BoomerChiao/Arduino_Air-Quality-Monitor/Jpg/3D_casing_A.png

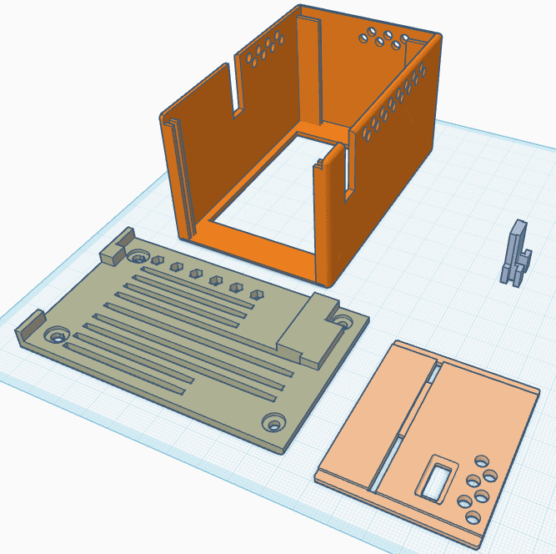
Jpg/3D_casing_A.png
