BoomerChiao/Arduino_Air-Quality-Monitor/Jpg/3D_casing_B.png

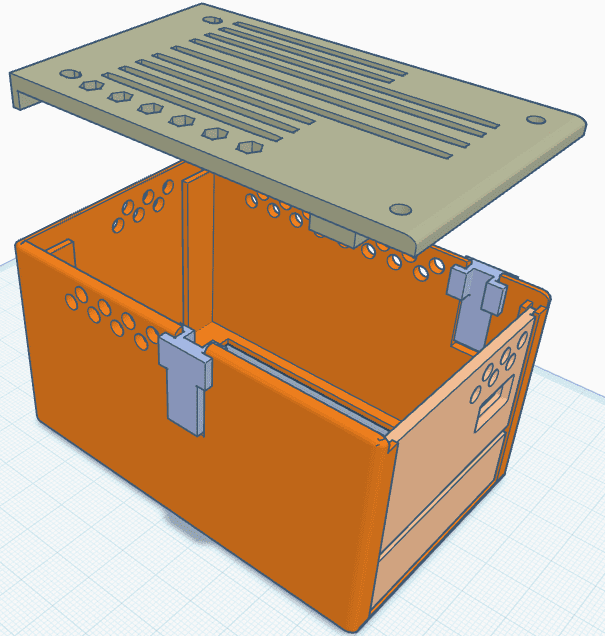
Jpg/3D_casing_B.png
