BoomerChiao/Arduino_Air-Quality-Monitor/Jpg/3D_casing_C.png

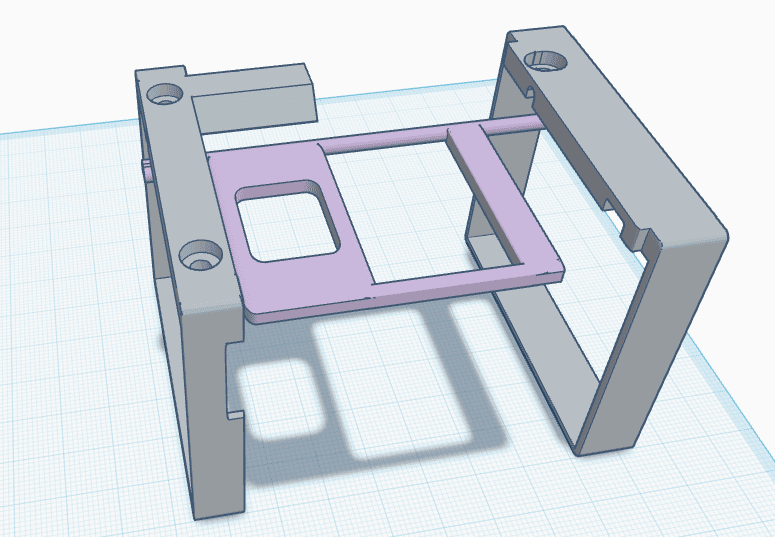
Jpg/3D_casing_C.png
