BoomerChiao/Arduino_Air-Quality-Monitor/Jpg/3D_casing_D.png

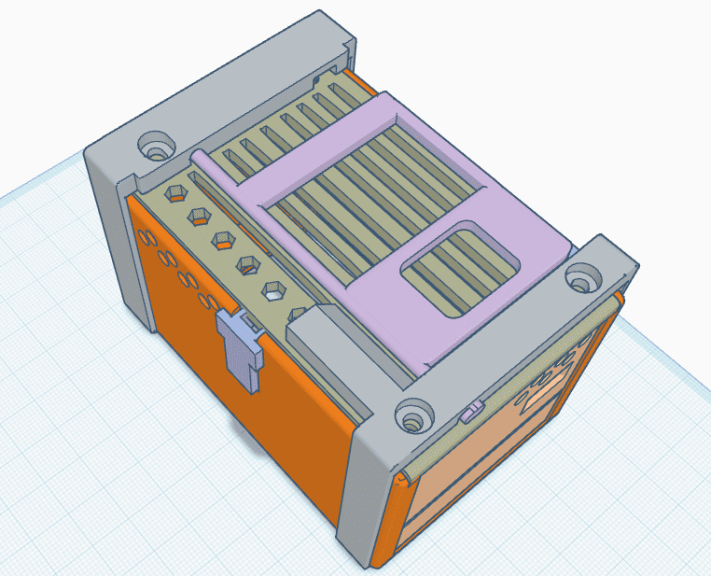
Jpg/3D_casing_D.png
