BoomerChiao/Arduino_Air-Quality-Monitor/Jpg/3D_casing_E.png

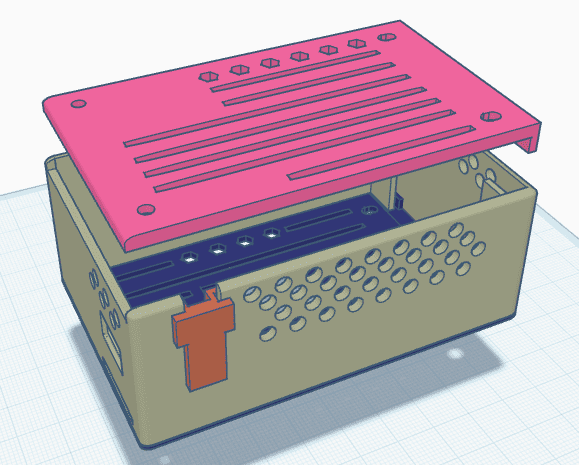
Jpg/3D_casing_E.png
