BoomerChiao/Arduino_Air-Quality-Monitor/Jpg/3D_casing_F.png

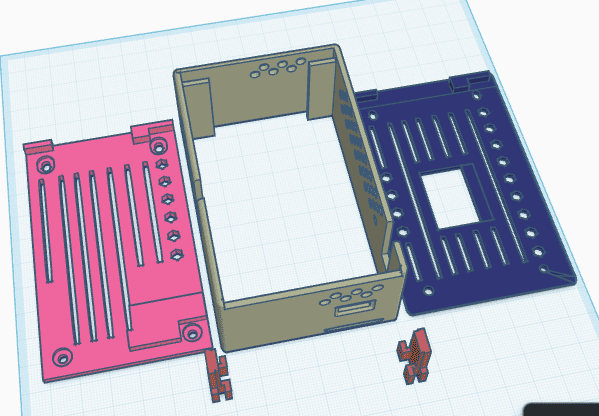
Jpg/3D_casing_F.png
