BoomerChiao/Arduino_Air-Quality-Monitor/Jpg/AHT20.png

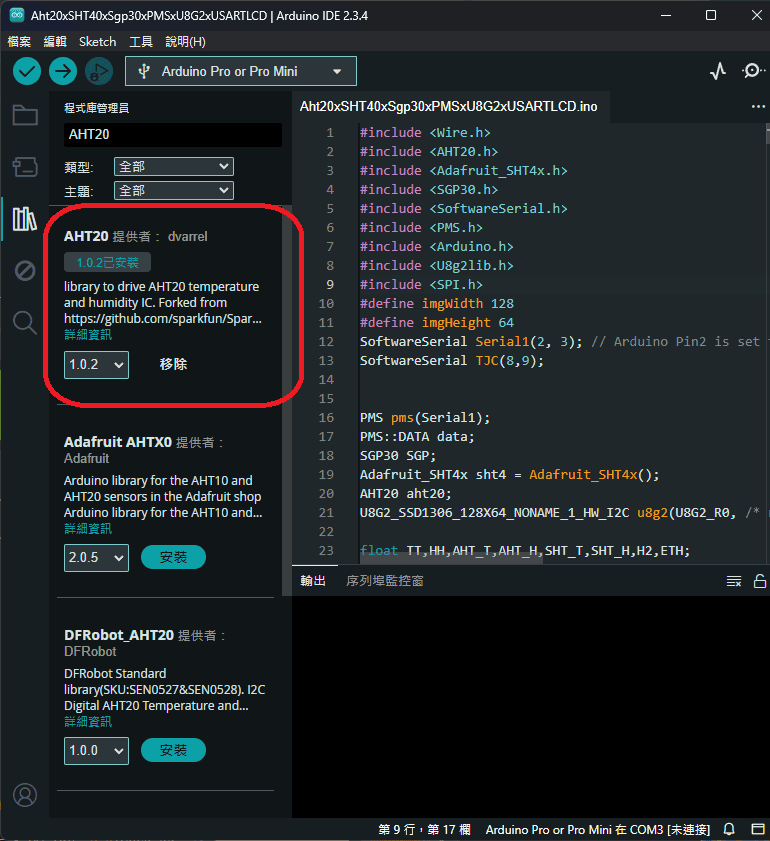
Jpg/AHT20.png
