BoomerChiao/Arduino_Air-Quality-Monitor/Jpg/DEMO/LCD_3d_A.png

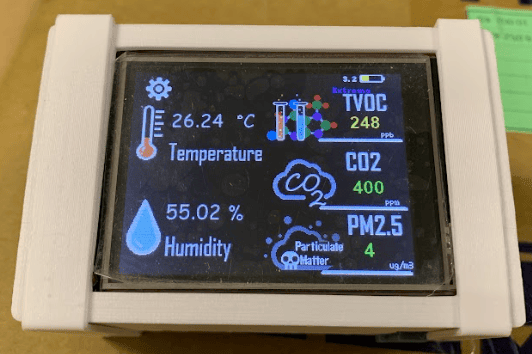
Jpg/DEMO/LCD_3d_A.png
