BoomerChiao/Arduino_Air-Quality-Monitor/Jpg/DEMO/LCD_3d_B.png

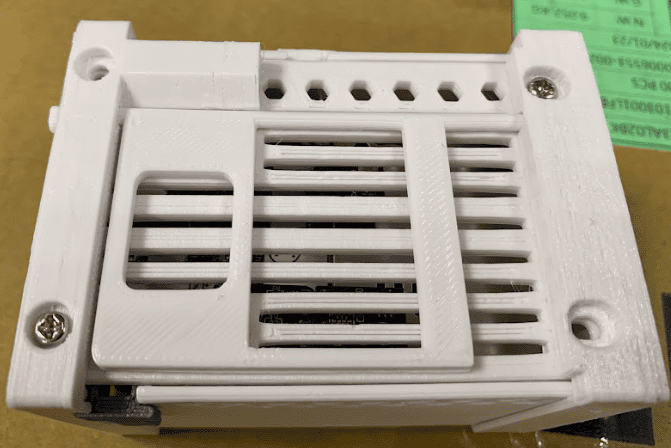
Jpg/DEMO/LCD_3d_B.png
