BoomerChiao/Arduino_Air-Quality-Monitor/Jpg/DEMO/LCD_3d_C.png

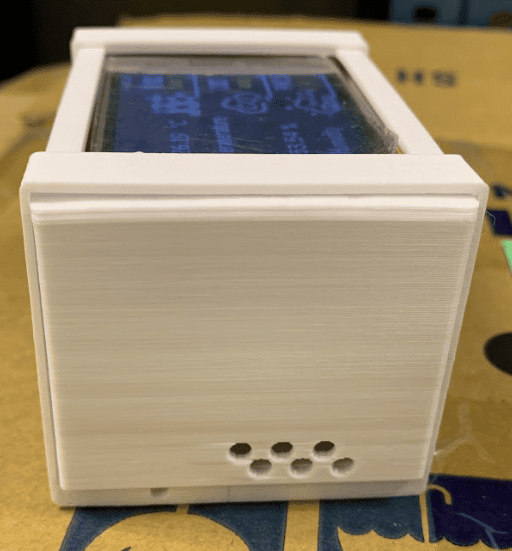
Jpg/DEMO/LCD_3d_C.png
