BoomerChiao/Arduino_Air-Quality-Monitor/Jpg/DEMO/LCD_3d_CD.png

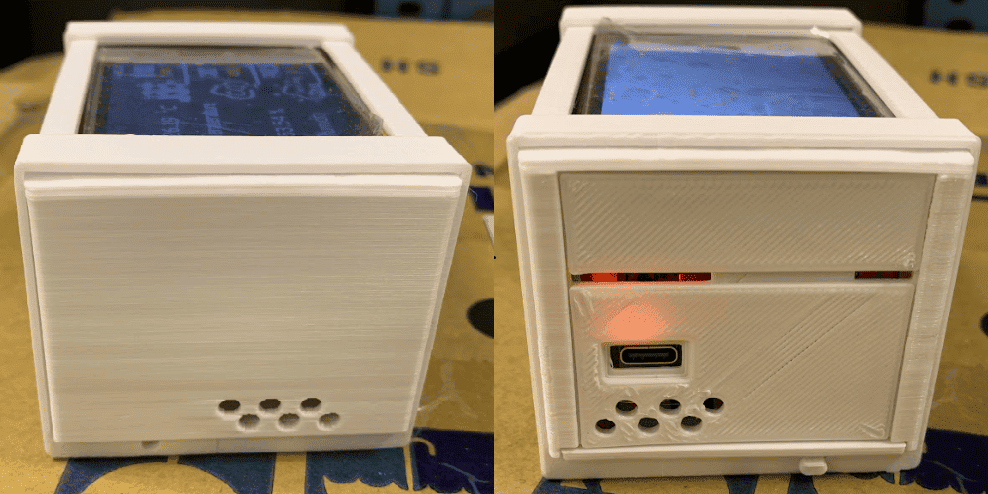
Jpg/DEMO/LCD_3d_CD.png
