BoomerChiao/Arduino_Air-Quality-Monitor/Jpg/DEMO/LCD_3d_D.png

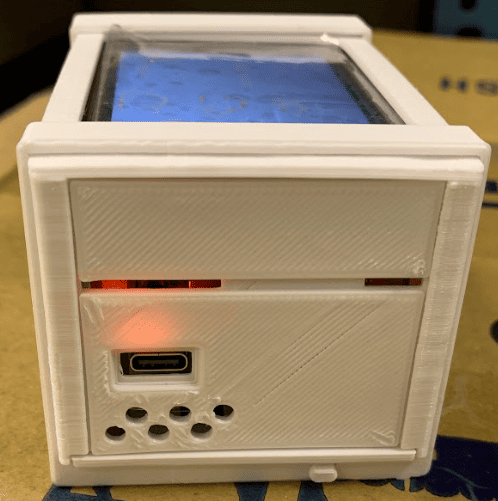
Jpg/DEMO/LCD_3d_D.png
