BoomerChiao/Arduino_Air-Quality-Monitor/Jpg/DEMO/LCD_3d_E.png

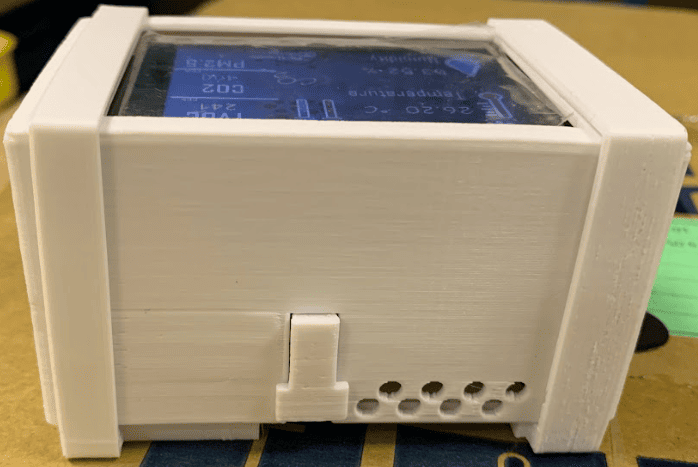
Jpg/DEMO/LCD_3d_E.png
