BoomerChiao/Arduino_Air-Quality-Monitor/Jpg/DEMO/LCD_3d_EF.png

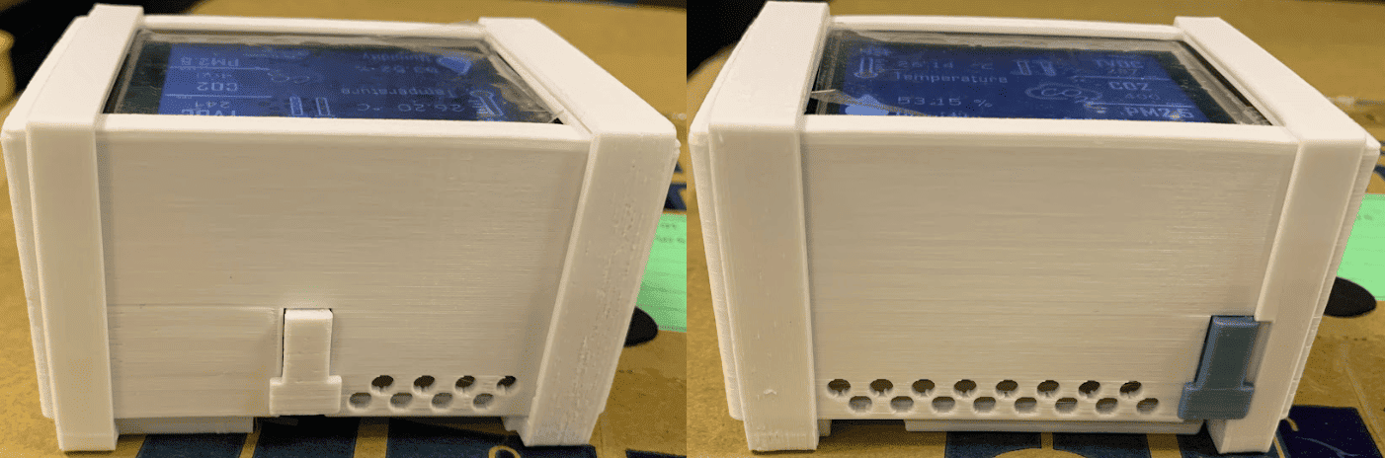
Jpg/DEMO/LCD_3d_EF.png
