BoomerChiao/Arduino_Air-Quality-Monitor/Jpg/DEMO/LCD_3d_F.png

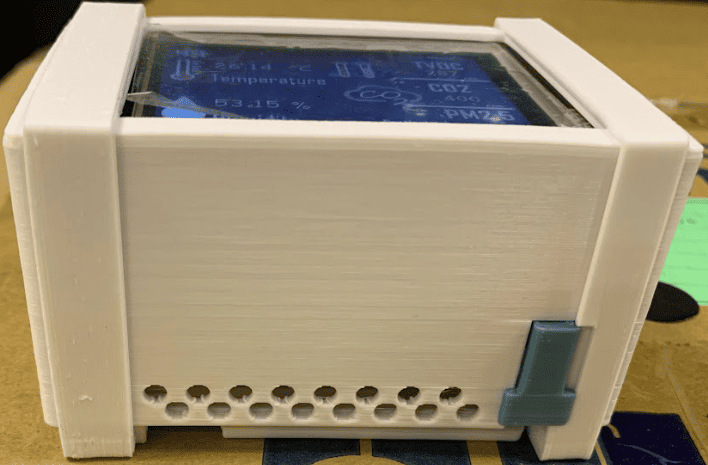
Jpg/DEMO/LCD_3d_F.png
