BoomerChiao/Arduino_Air-Quality-Monitor/Jpg/DEMO/LCD_3d_G.png

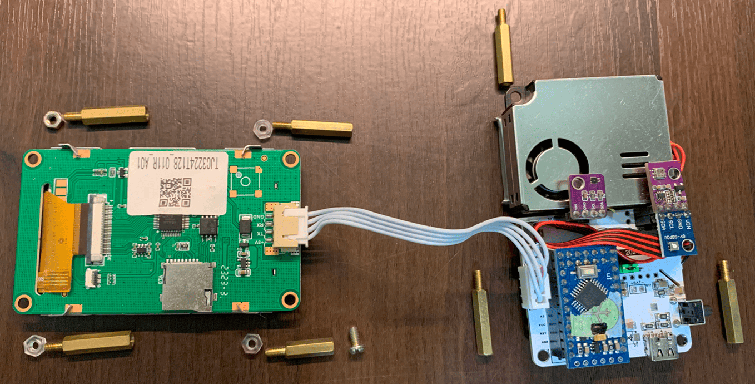
Jpg/DEMO/LCD_3d_G.png
