BoomerChiao/Arduino_Air-Quality-Monitor/Jpg/DEMO/LCD_3d_GA.png

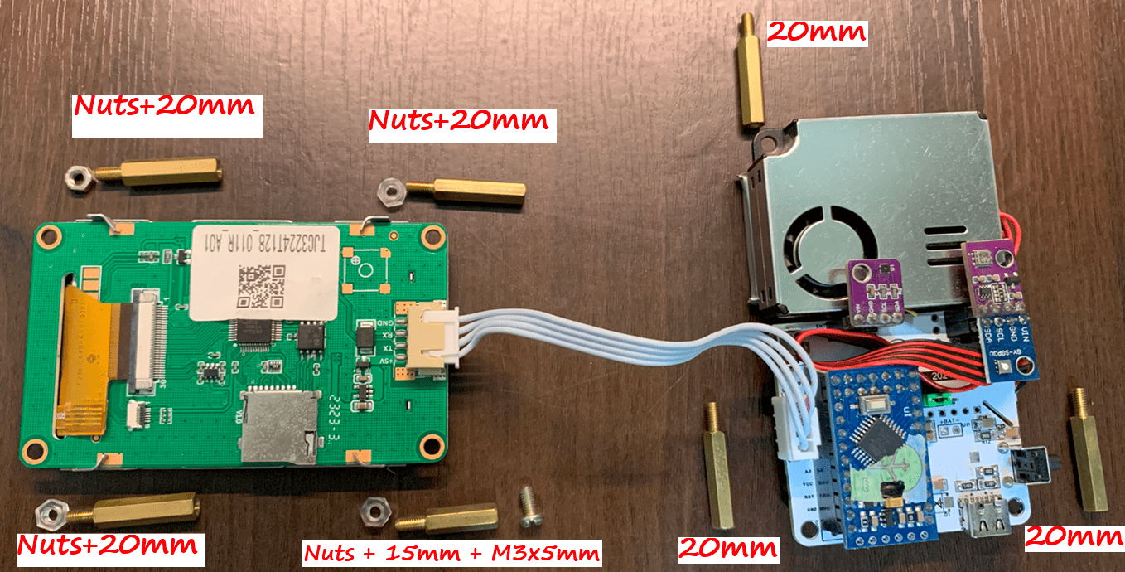
Jpg/DEMO/LCD_3d_GA.png
