BoomerChiao/Arduino_Air-Quality-Monitor/Jpg/DEMO/LCD_3d_H.png

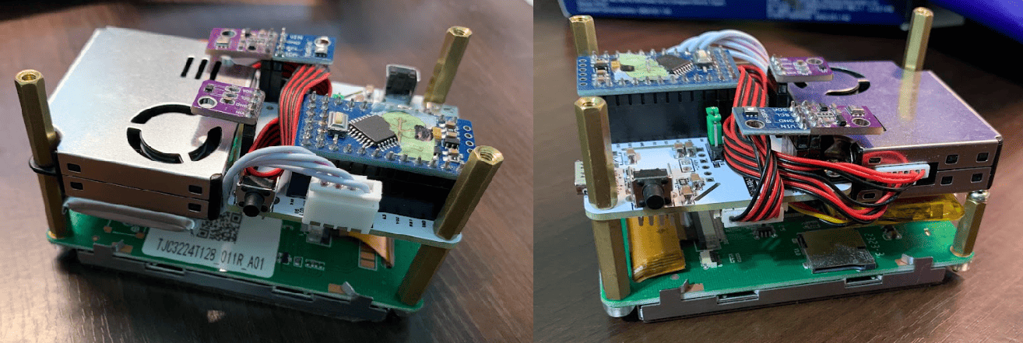
Jpg/DEMO/LCD_3d_H.png
