BoomerChiao/Arduino_Air-Quality-Monitor/Jpg/DEMO/LCD_A.png

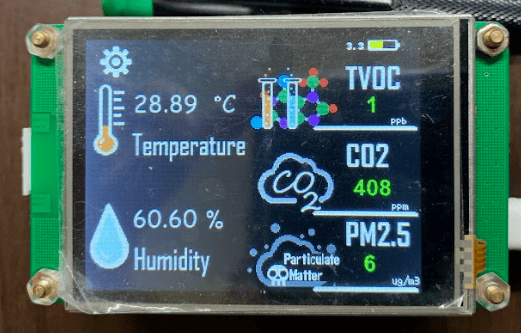
Jpg/DEMO/LCD_A.png
