BoomerChiao/Arduino_Air-Quality-Monitor/Jpg/DEMO/LCD_AB.png

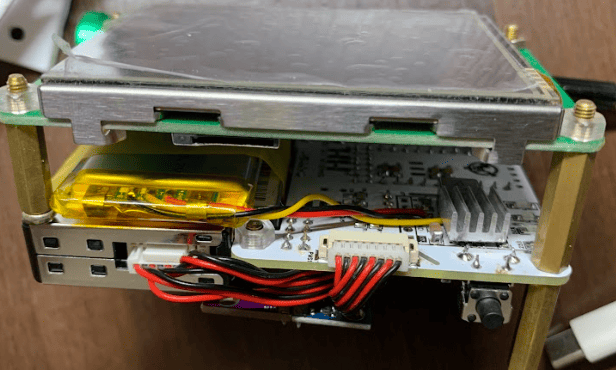
Jpg/DEMO/LCD_AB.png
