BoomerChiao/Arduino_Air-Quality-Monitor/Jpg/DEMO/LCD_B.png

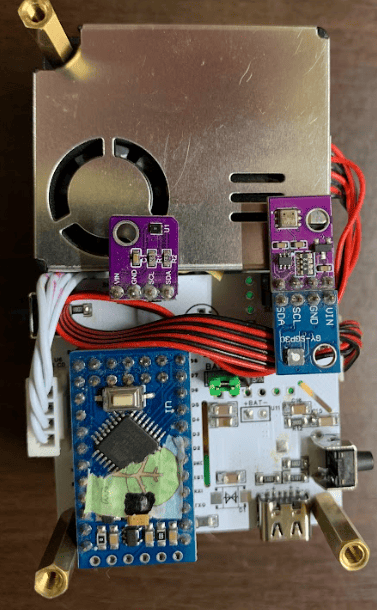
Jpg/DEMO/LCD_B.png
