BoomerChiao/Arduino_Air-Quality-Monitor/Jpg/DEMO/OLED_3d_A.png

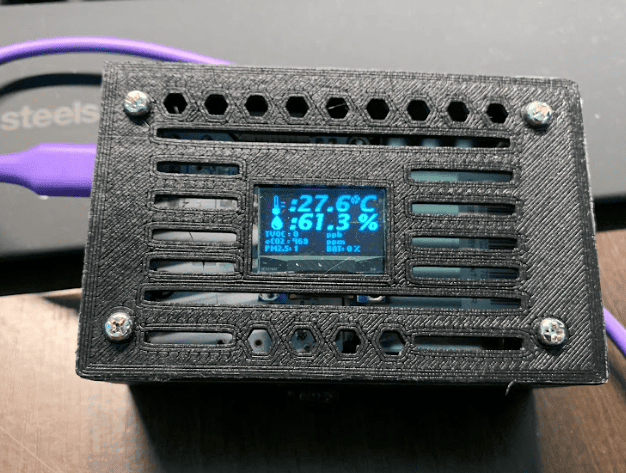
Jpg/DEMO/OLED_3d_A.png
