BoomerChiao/Arduino_Air-Quality-Monitor/Jpg/DEMO/OLED_3d_B.png

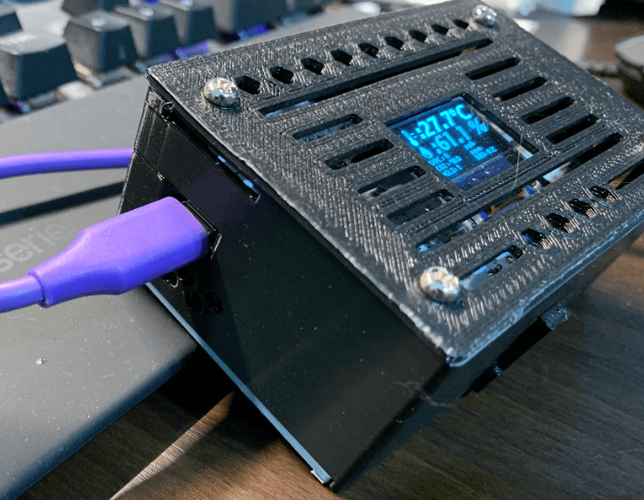
Jpg/DEMO/OLED_3d_B.png
