BoomerChiao/Arduino_Air-Quality-Monitor/Jpg/DEMO/OLED_3d_D.png

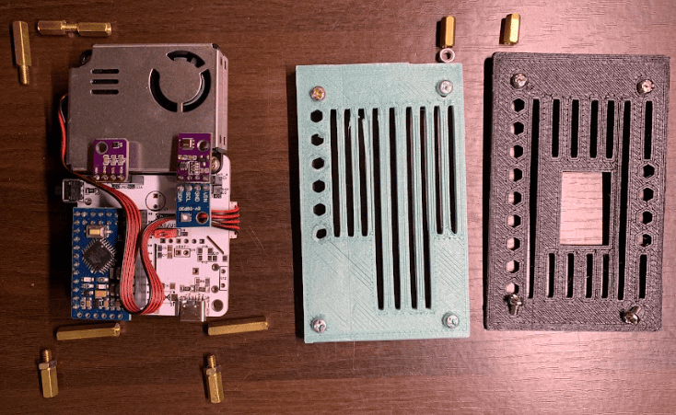
Jpg/DEMO/OLED_3d_D.png
