BoomerChiao/Arduino_Air-Quality-Monitor/Jpg/DEMO/OLED_3d_DA.png

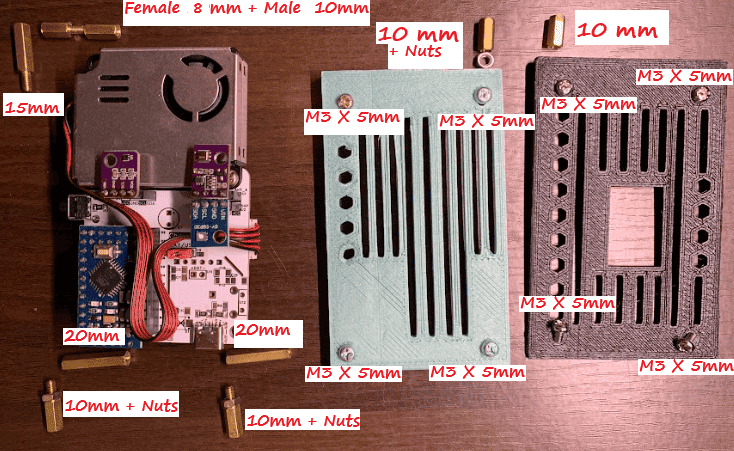
Jpg/DEMO/OLED_3d_DA.png
