BoomerChiao/Arduino_Air-Quality-Monitor/Jpg/DEMO/OLED_3d_E.png

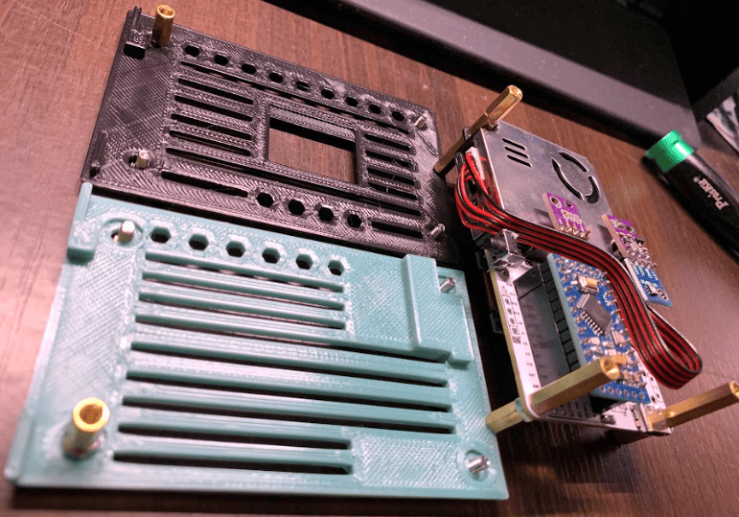
Jpg/DEMO/OLED_3d_E.png
