BoomerChiao/Arduino_Air-Quality-Monitor/Jpg/DEMO/OLED_A.png

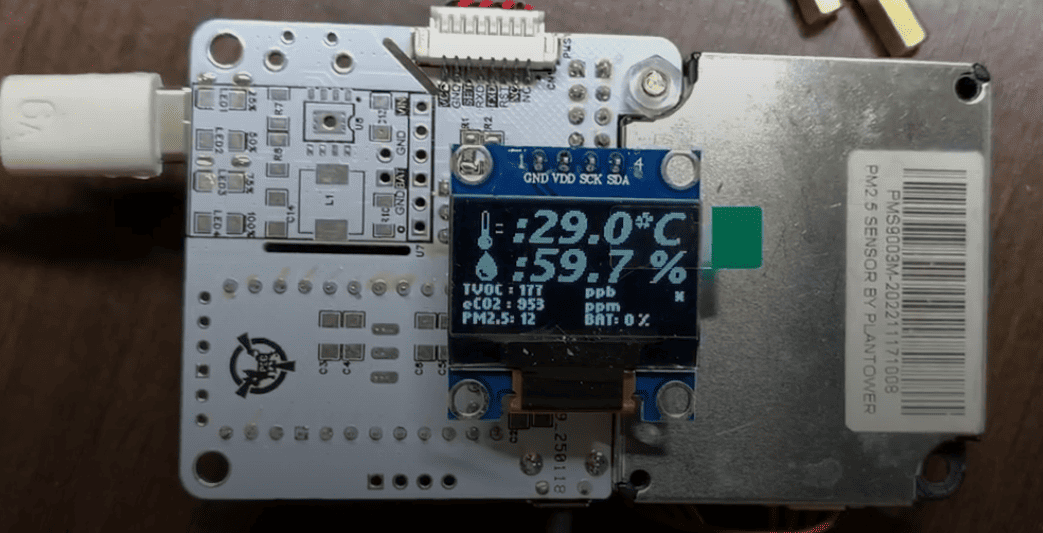
Jpg/DEMO/OLED_A.png
