BoomerChiao/Arduino_Air-Quality-Monitor/Jpg/DEMO/OLED_B.png

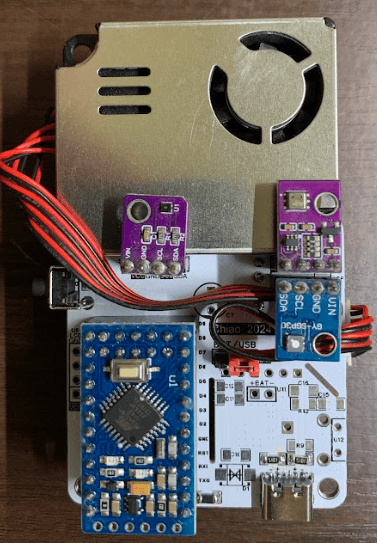
Jpg/DEMO/OLED_B.png
