BoomerChiao/Arduino_Air-Quality-Monitor/Jpg/DEMO/OLED_LCD_A.png

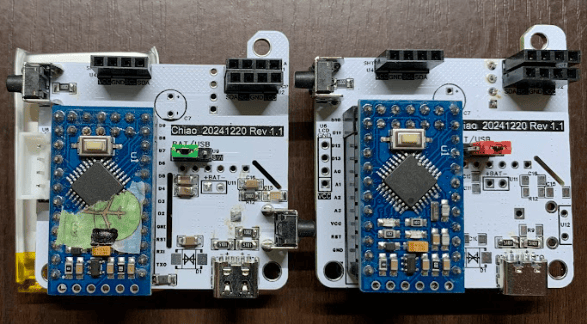
Jpg/DEMO/OLED_LCD_A.png
