BoomerChiao/Arduino_Air-Quality-Monitor/Jpg/DEMO/uiux.png

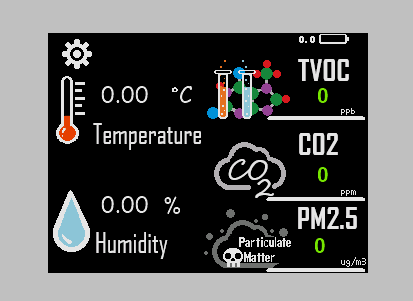
Jpg/DEMO/uiux.png
