BoomerChiao/Arduino_Air-Quality-Monitor/Jpg/DEMO/uiux_A.png

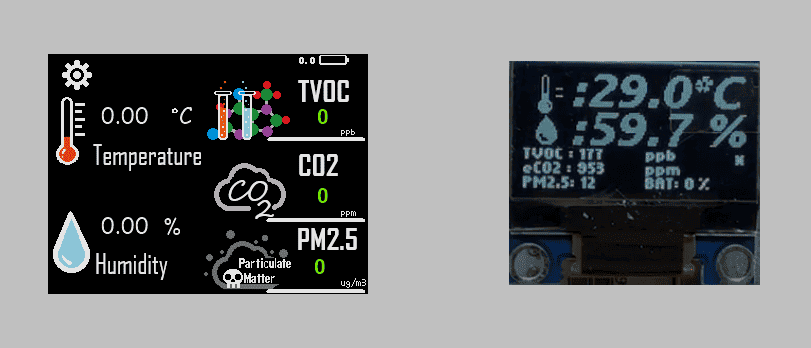
Jpg/DEMO/uiux_A.png
