BoomerChiao/Arduino_Air-Quality-Monitor/Jpg/DEMO/uiux_B.png

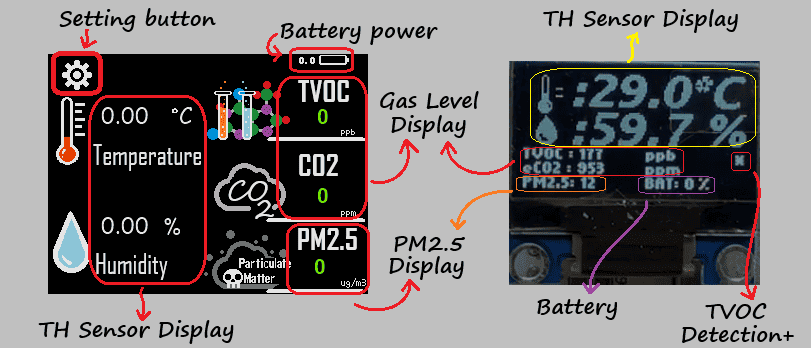
Jpg/DEMO/uiux_B.png
