BoomerChiao/Arduino_Air-Quality-Monitor/Jpg/DEMO/uiux_oled.png

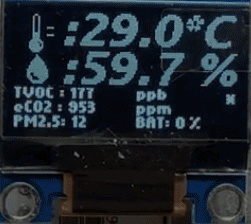
Jpg/DEMO/uiux_oled.png
