BoomerChiao/Arduino_Air-Quality-Monitor/Jpg/PCB_A.png

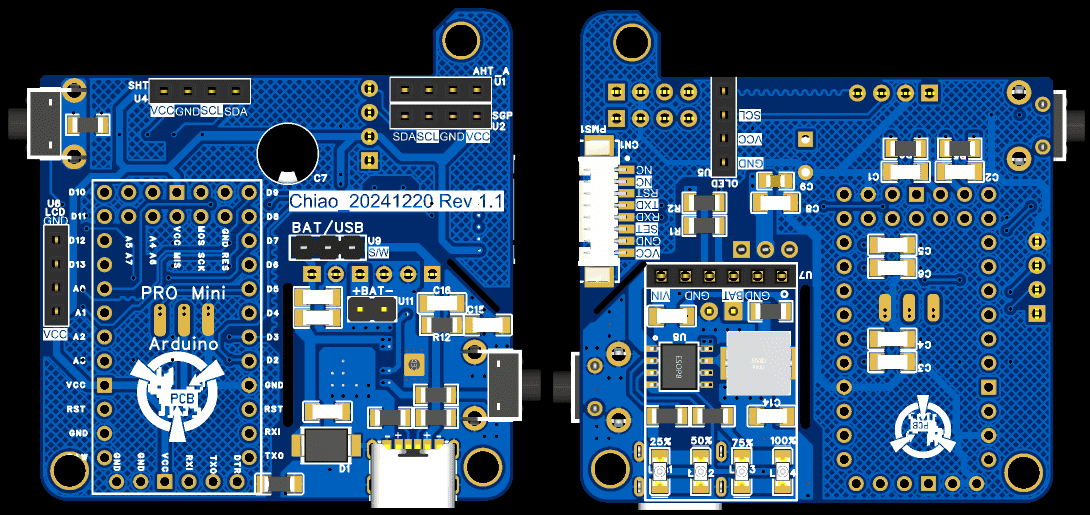
Jpg/PCB_A.png
