BoomerChiao/Arduino_Air-Quality-Monitor/Jpg/PCBL_A.png

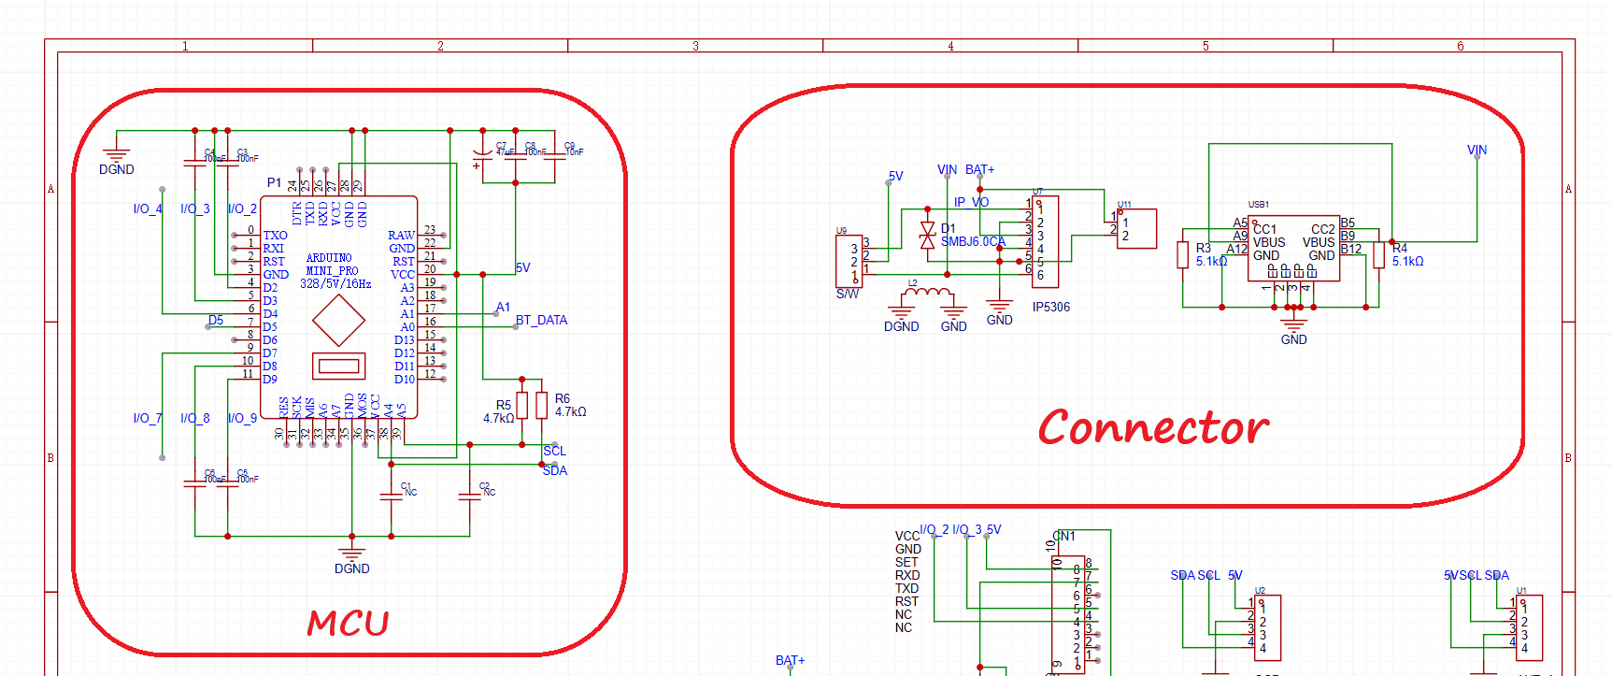
Jpg/PCBL_A.png
