BoomerChiao/Arduino_Air-Quality-Monitor/Jpg/PCBL_B.png

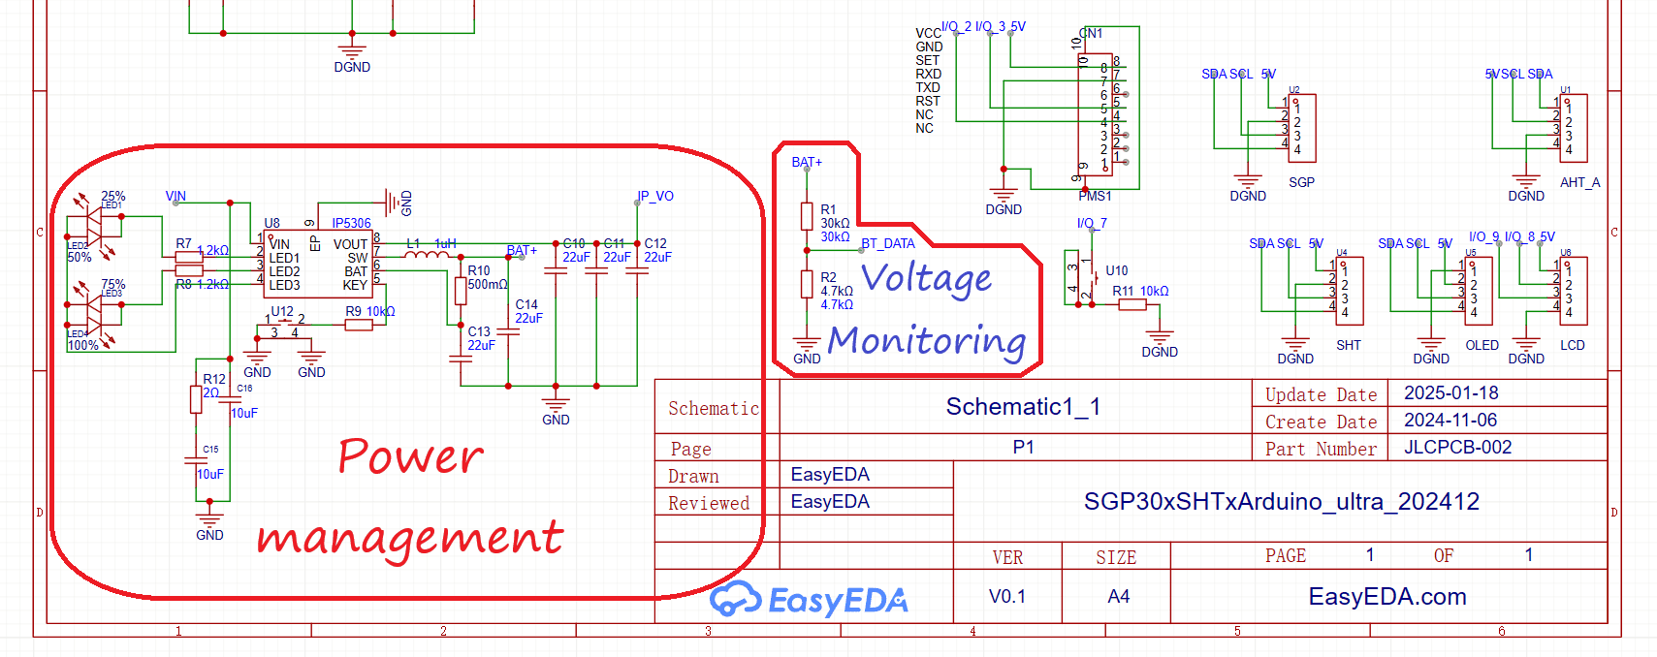
Jpg/PCBL_B.png
