BoomerChiao/Arduino_Air-Quality-Monitor/Jpg/PMS.png

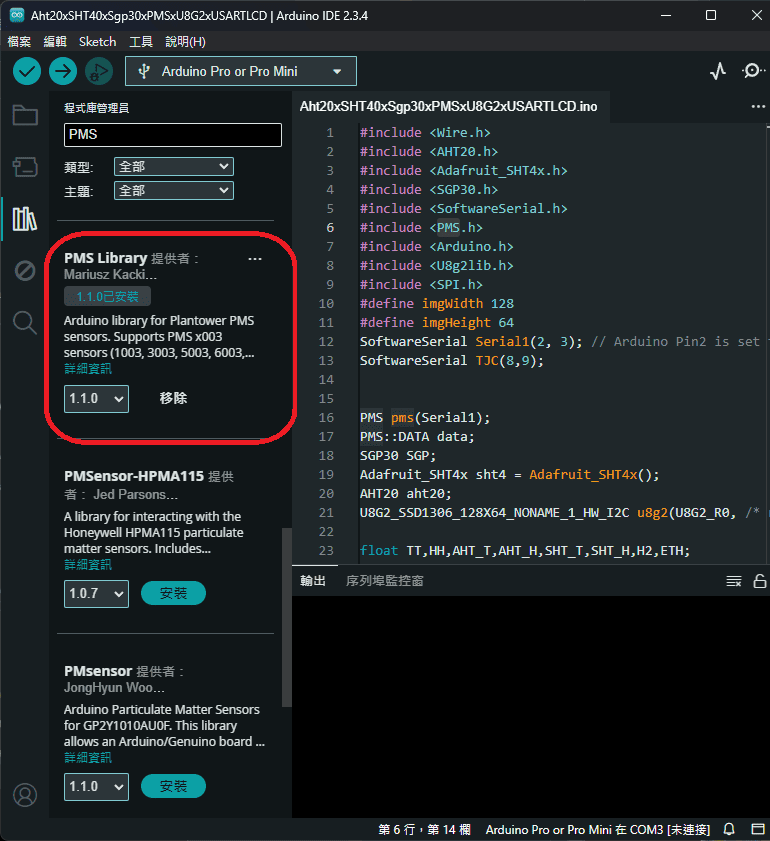
Jpg/PMS.png
