BoomerChiao/Arduino_Air-Quality-Monitor/Jpg/USART_B.png

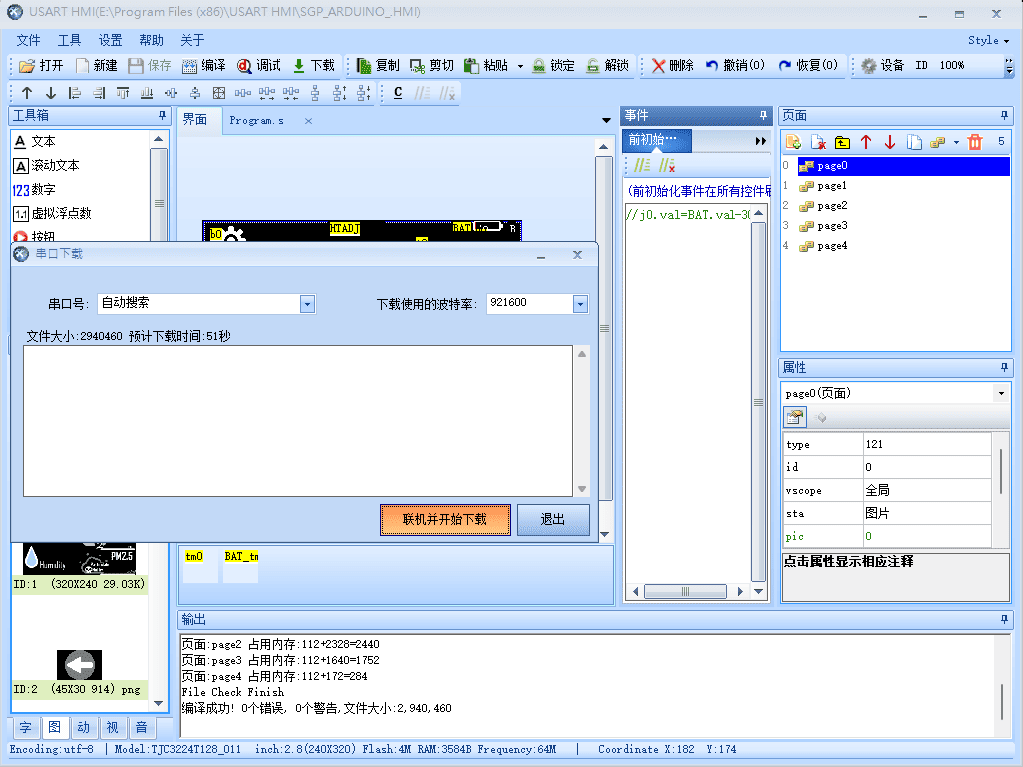
Jpg/USART_B.png
