BoomerChiao/Arduino_Air-Quality-Monitor/Jpg/USART_C.png

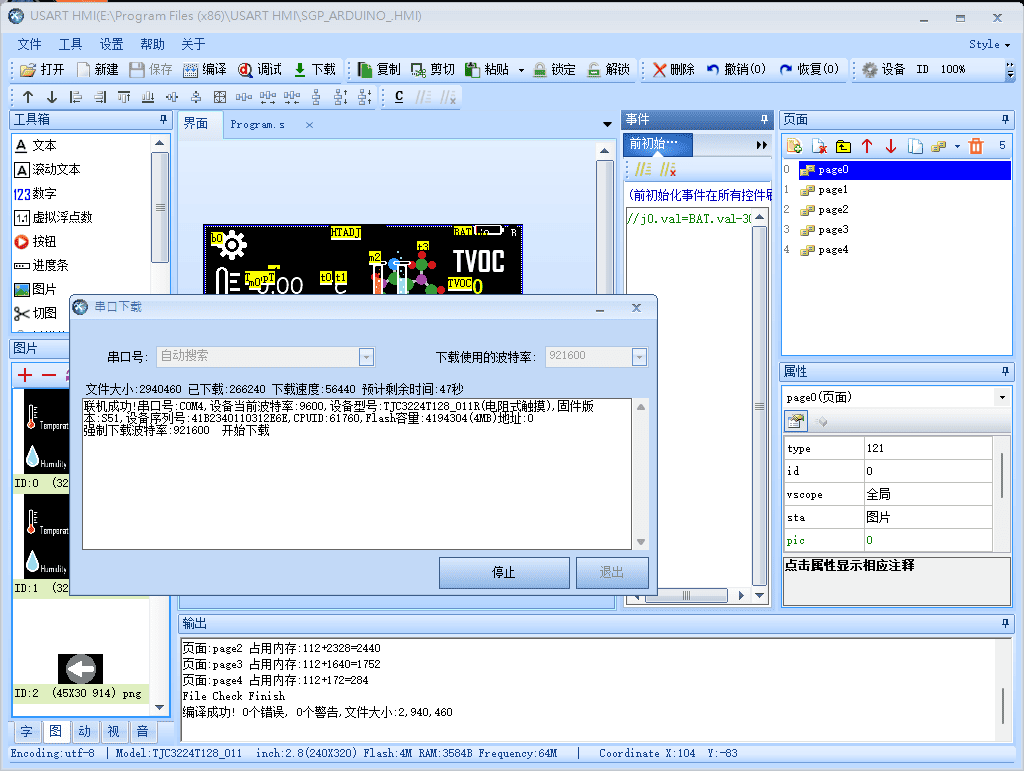
Jpg/USART_C.png
