BoomerChiao/Arduino_Air-Quality-Monitor/Jpg/USART_D.png

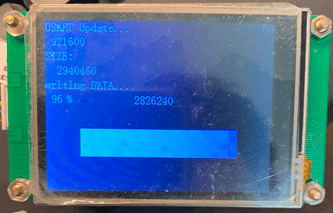
Jpg/USART_D.png
