BoomerChiao/Arduino_Air-Quality-Monitor/Jpg/Materials_A.png

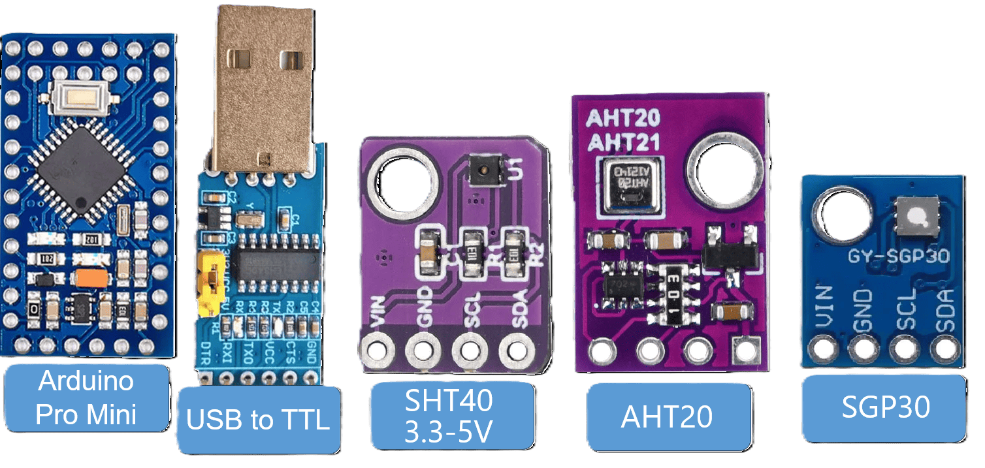
Jpg/Materials_A.png
