BoomerChiao/Arduino_Air-Quality-Monitor/Jpg/Materials_B.png

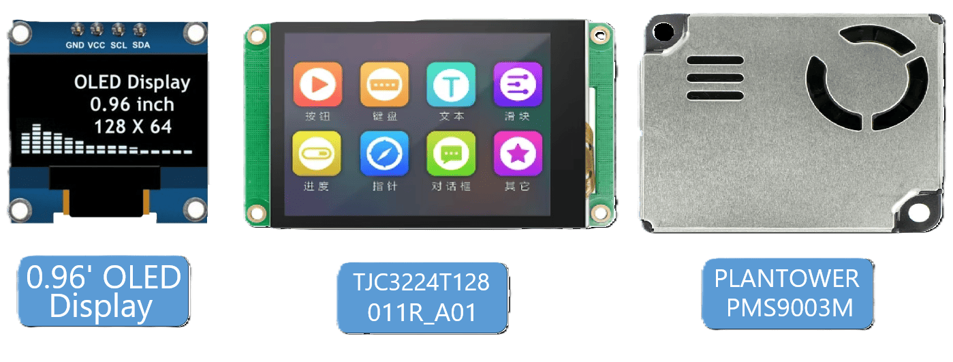
Jpg/Materials_B.png
