BoomerChiao/Arduino_Air-Quality-Monitor/Jpg/Materials_D.png

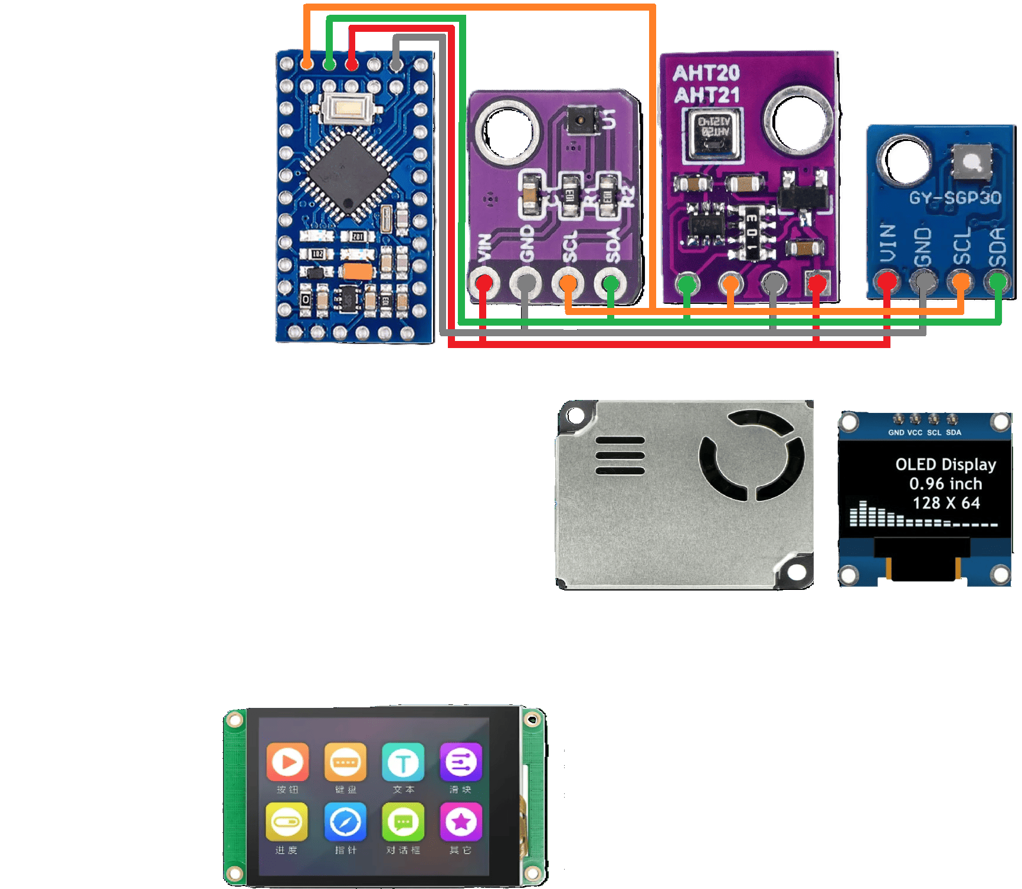
Jpg/Materials_D.png
