BoomerChiao/Arduino_Air-Quality-Monitor/Jpg/Materials_E.png

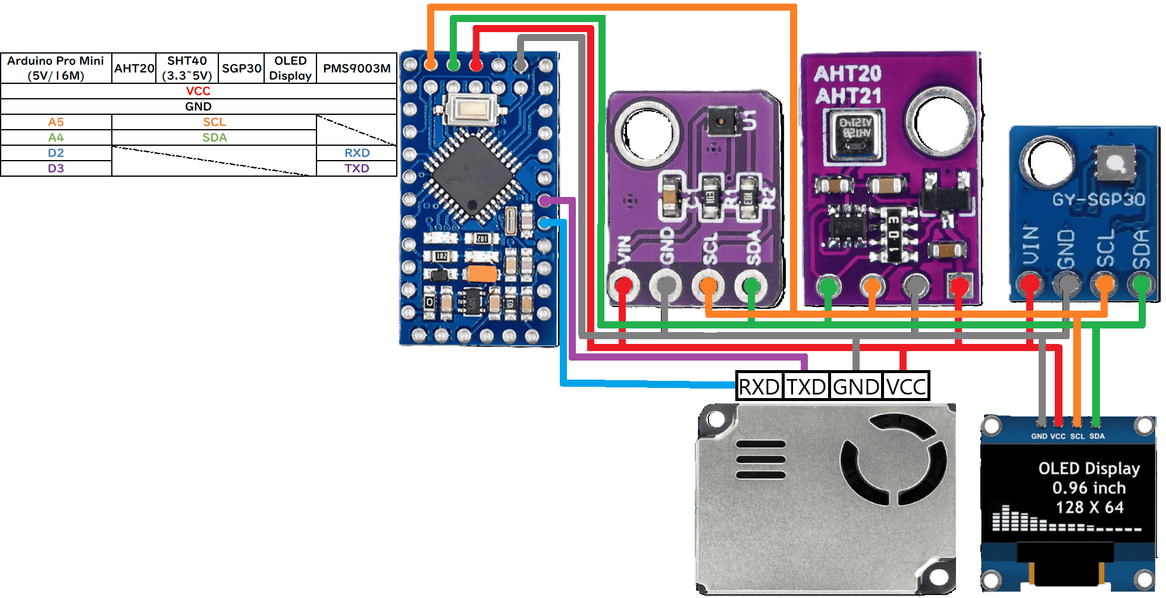
Jpg/Materials_E.png
