BoomerChiao/Arduino_Air-Quality-Monitor/Jpg/Materials_F.png

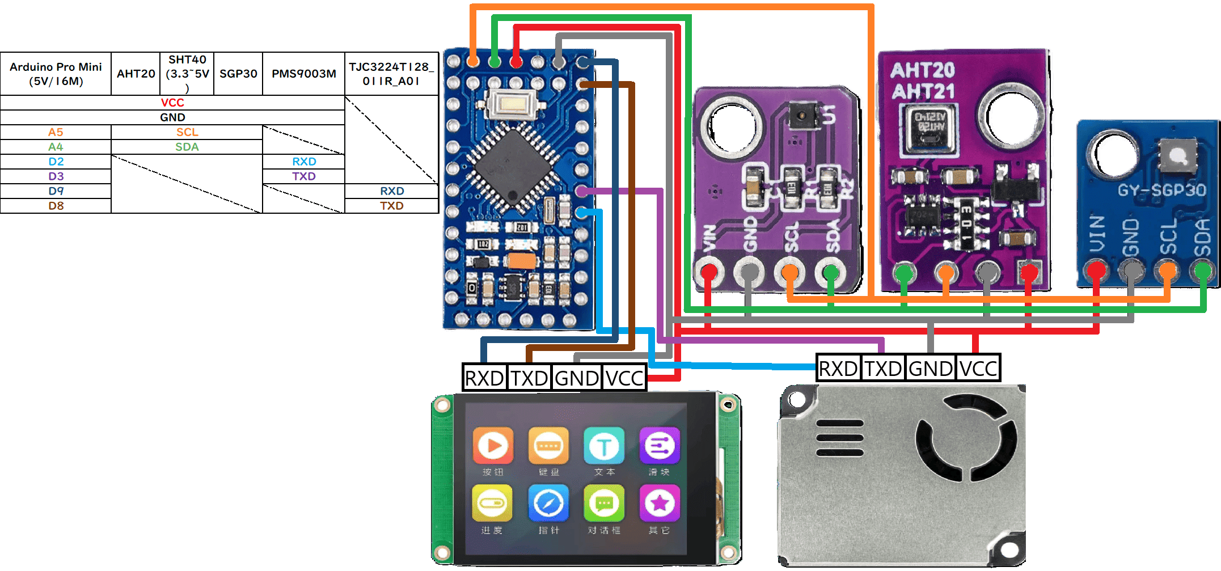
Jpg/Materials_F.png
