BoomerChiao/Arduino_Air-Quality-Monitor/Jpg/DEMO/LCD_TEST.png

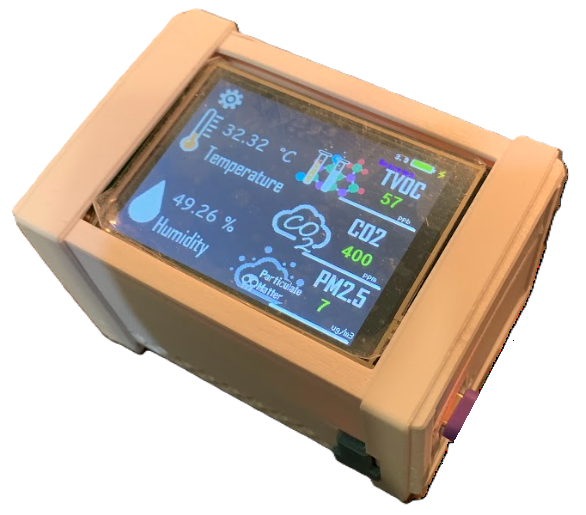
Jpg/DEMO/LCD_TEST.png
