BoomerChiao/Arduino_Air-Quality-Monitor/Jpg/DEMO/LCDandOLED_TEST.png

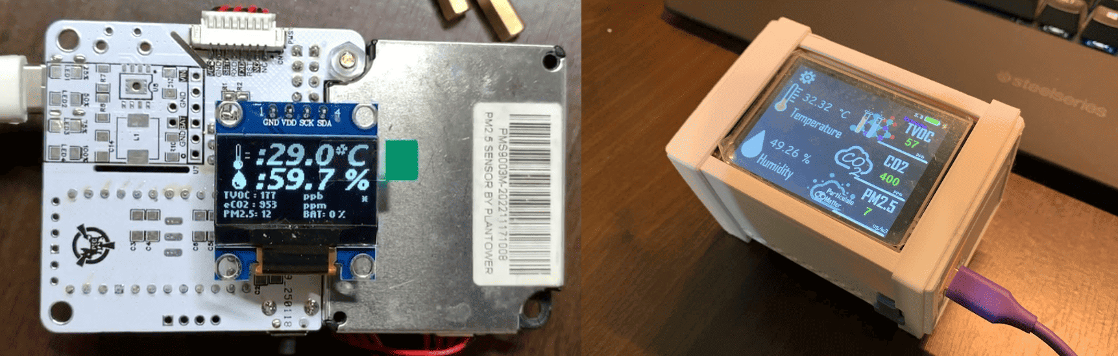
Jpg/DEMO/LCDandOLED_TEST.png
